dartcom/ssd2828-dev/imgs/IMG_5381.JPG

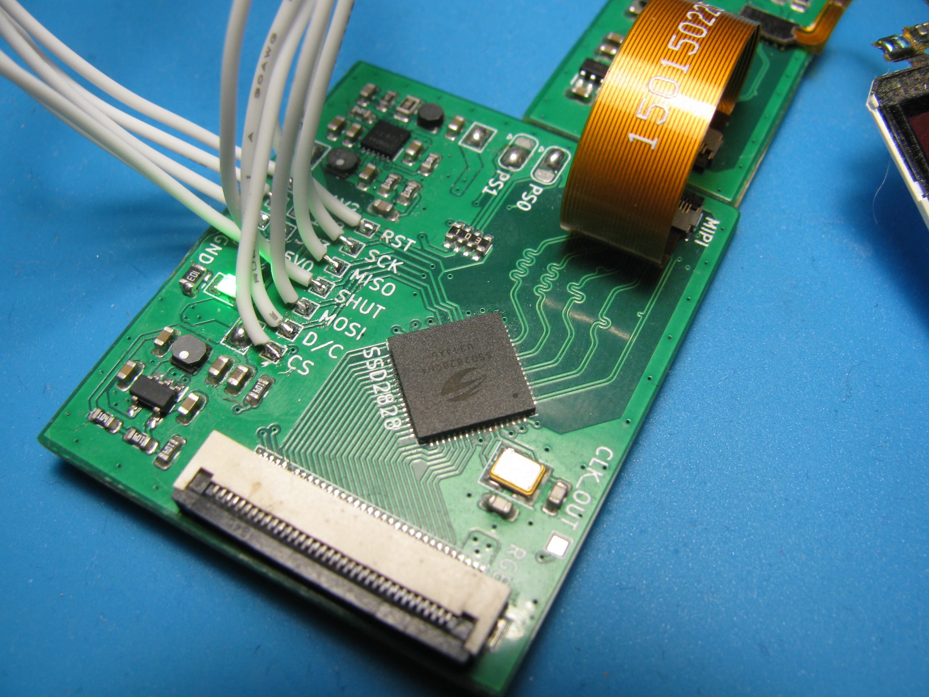
imgs/IMG_5381.JPG
